thryothorus/pcb_wheel_rfm69_counter/avr_code/defines.c

#include "defines.h"

 unsigned char DATA_BUFFER_65[64];
 uint8_t DATA_BUFFER_7[7];
 uint8_t DATA_BUFFER_254[254];
 unsigned char DATA_BUFFER_20[20];
 ndef_message NDEF_MSG;
 trimmed_string_struct TRIMMED_STRING;
 identifier_results IDENTIFIER;
 tx_rx_data_struct TX_DATA;
 tx_rx_data_struct RX_DATA;
 time_struct TIME;
